fellesverkstedet/hat-systems/Bridge/BRIDGE_v0.9_no_dogbones_sheet_2of2.dxf

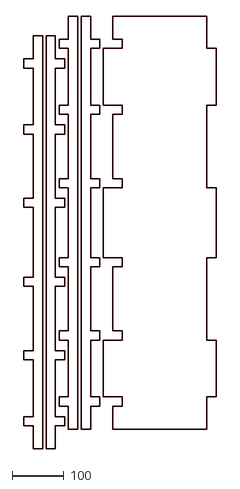
[picture p26: CAD file, 2016-01-22]
Bridge/BRIDGE_v0.9_no_dogbones_sheet_2of2.dxf
372.0 x 838.0
