fellesverkstedet/hat-systems/Drawer_big_one.stl

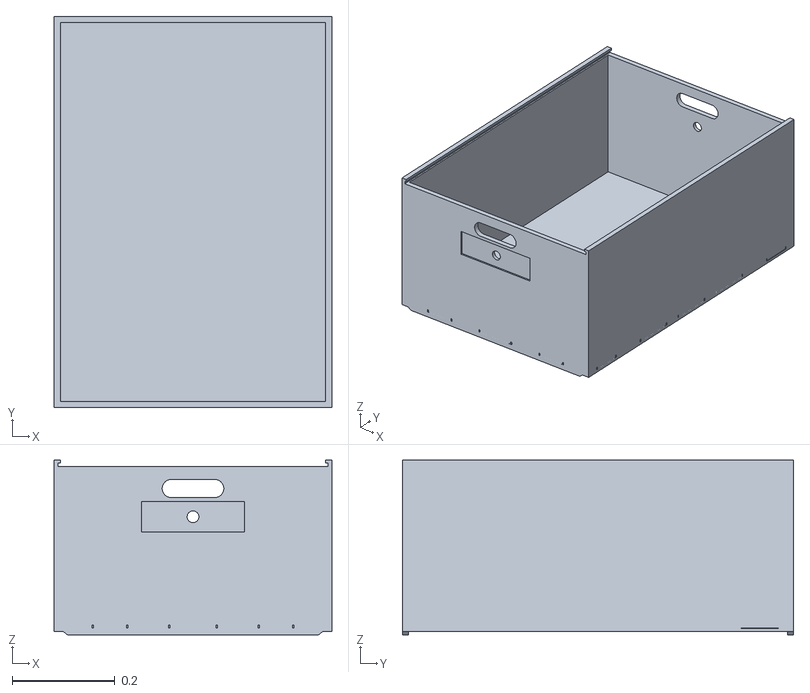
[picture p27: CAD file, 2016-01-22]
Drawer_big_one.stl
0.54 x 0.76 x 0.339
