fellesverkstedet/hat-systems/Big_One_drawer/BIG_ONE_Drawer_6mm_dogbones.dxf

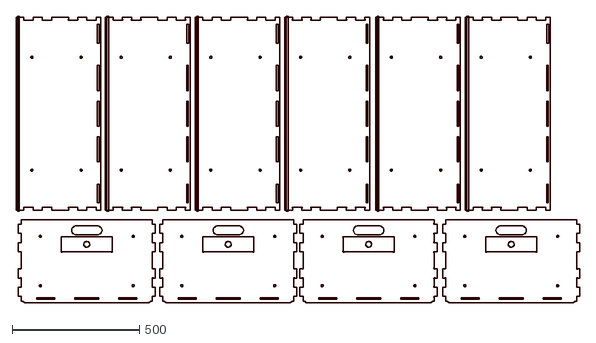
[picture p28: CAD file, 2016-01-22]
Big_One_drawer/BIG_ONE_Drawer_6mm_dogbones.dxf
2217.9 x 1126.4
