fellesverkstedet/hat-systems/Drawer_regular.stl

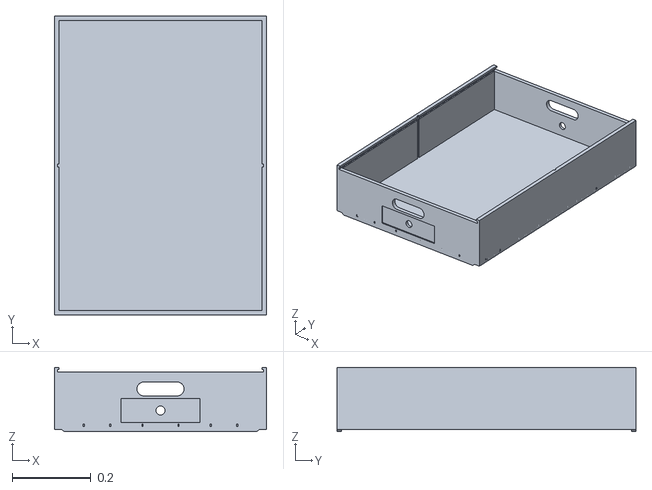
[picture p29: CAD file, 2016-01-22]
Drawer_regular.stl
0.54 x 0.76 x 0.164
